Kwanic/ECE445/boards/PPG_layout.png

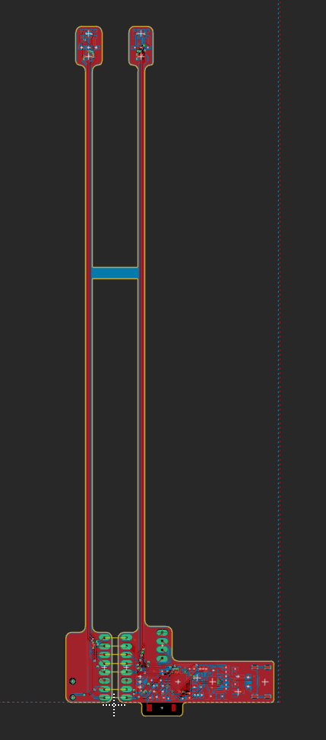
boards/PPG_layout.png
