Kwanic/ECE445/notebooks/Mark/MAX86141_breakout.png

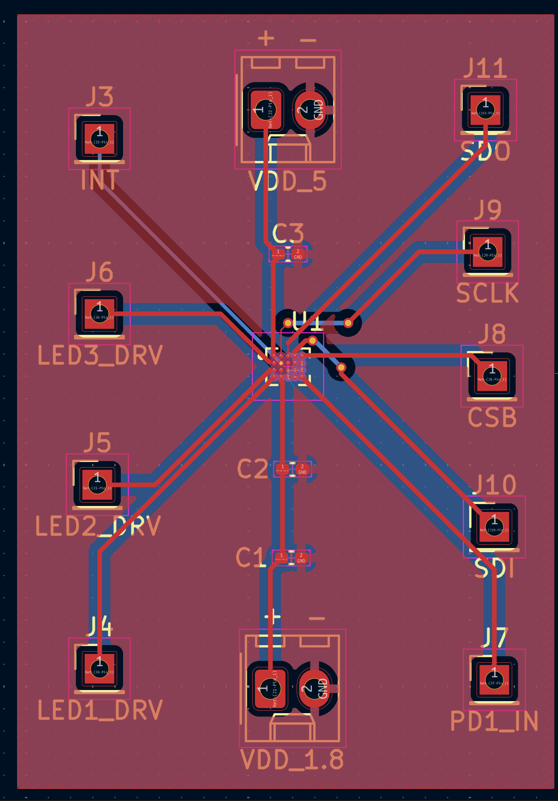
notebooks/Mark/MAX86141_breakout.png
